CFSebastian/introduction-to-robotics-project/Media/SchemaTelecomanda.PNG

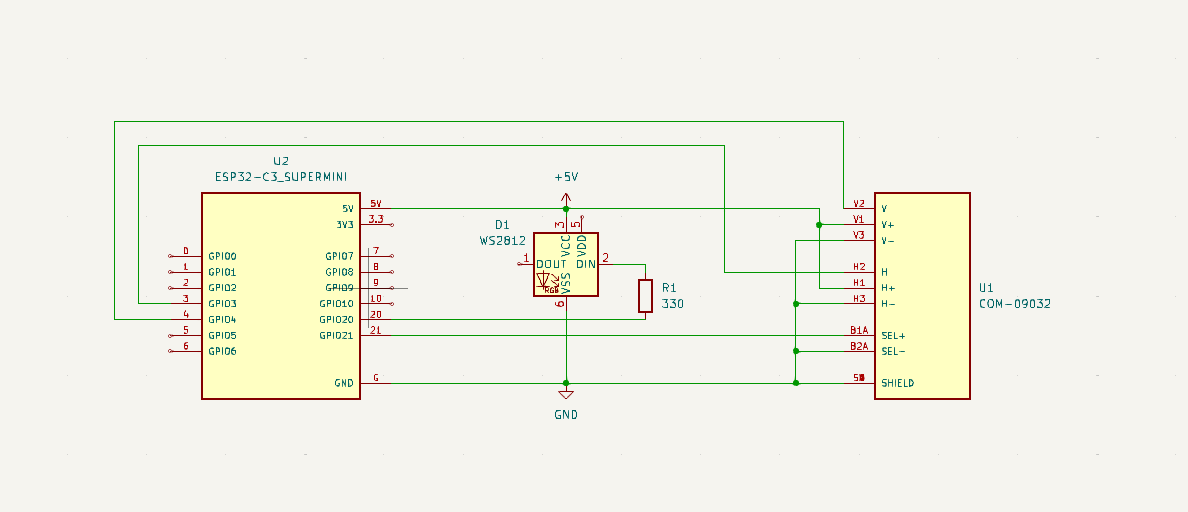
Media/SchemaTelecomanda.PNG
